dillacorn/QiDi_Plus4/Fluidd/gcode_macro.cfg

# QIDI Plus4 V1.0.0

[gcode_macro _CG28]
description: Safely establish XYZ homing only when needed
gcode:
    {% set homed = printer.toolhead.homed_axes %}

    # If either XY axis is unknown, use QIDI's complete safe
    # X/Y/X and Z homing sequence.
    {% if "x" not in homed or "y" not in homed %}
        G28

    # When XY is already established, home only Z.
    {% elif "z" not in homed %}
        G28 Z
    {% endif %}

[gcode_macro _CXY28]
description: Safely establish XY homing only when needed. Never homes Z.
gcode:
    {% set homed = printer.toolhead.homed_axes %}

    # If either XY axis is unknown, always preserve QIDI's
    # safe X-first X/Y/X homing sequence.
    {% if "x" not in homed or "y" not in homed %}
        G28 X
        G28 Y
        G28 X
    {% endif %}

[gcode_macro zoffset]
gcode:
    SET_GCODE_OFFSET Z={printer.probe.last_z_result} MOVE=1

# Z-offset test helper
[gcode_macro test_zoffset]
gcode:
    G28
    get_zoffset
    G1 X{150 - printer.probe["x_offset"]} Y{150 - printer.probe["y_offset"]} F9000
    G1 Z10 F600
    probe
    M400
    G4 P5000
    G1 Z10 F600

[gcode_macro move_subzoffset]
gcode:
    {% set z = printer.probe.last_z_result|float %}
    {% set z_min = printer.configfile.settings['stepper_z'].position_min|float %}

    {% if z < (z_min + 0.10) %}
        { action_raise_error("Refusing move_subzoffset: suspicious probe result " ~ z ~ " is too close to position_min " ~ z_min) }
    {% endif %}

    G1 Z{z} F600

[gcode_macro get_zoffset]
gcode:
    # TOGGLE_CHAMBER_FAN
    G1 Z10 F600
    Z_VIBRATE
    QIDI_PROBE_PIN_1
    M204 S50
    G4 P500
    probe probe_speed=5 lift_speed=18 samples=5 sample_retract_dist=10
    move_subzoffset
    M114
    {% set p = (-0.15 + printer.gcode_move.homing_origin.z)|float %}
    SET_KINEMATIC_POSITION Z={p}
    G1 Z30 F600
    QIDI_PROBE_PIN_2
    M204 S8800
    # TOGGLE_CHAMBER_FAN

[gcode_macro save_zoffset]
gcode:
    # {% if printer.gcode_move.homing_origin.z < 0.5 %}
    #    SAVE_VARIABLE VARIABLE=z_offset VALUE={printer.gcode_move.homing_origin.z}
    # {% endif %}

[gcode_macro set_zoffset]        
gcode:
    {% set z = printer.save_variables.variables.z_offset %}
    SET_GCODE_OFFSET Z={z} MOVE=0

# Power-loss recovery nozzle clear.
[gcode_macro CLEAR_NOZZLE_PLR]
gcode:
    {% set hotendtemp = params.HOTEND|default(250)|int %}
    {% if (printer.gcode_move.position.z ) < 35 %}
        G1 Z35 F900
    {% else %}
        G91
        G1 Z{5} F900 
        G90
    {% endif %}
    G1 X56 F12000
    G1 Y310 F12000
    G1 Y324 F600
    G1 X95 F600
    M400

    M106 S0
    M109 S{hotendtemp}

    G92 E0
    G1 E5 F50
    G92 E0
    G1 E80 F200
    G92 E0
    G1 E-2 F200
    G4 P300

    M106 S255
    G1 Y316 F30000
    G1 Y320 F3000
    G1 Y316 F30000
    G1 Y320 F3000
    G1 Y316 F30000
    G1 Y320 F3000
    G1 Y316 F12000
    G1 Y312 F600

[gcode_macro CLEAR_NOZZLE]
gcode:
    {% set hotendtemp = params.HOTEND|default(250)|int %}
    {% set purge = params.PURGE|default(1)|int %}
    {% if (printer.gcode_move.position.z ) < 35 %}
        G1 Z35 F900
    {% else %}
        G91
        G1 Z{5} F900 
        G90
    {% endif %}
    G1 X56 F12000
    G1 Y310 F12000
    G1 Y324 F600
    G1 X95 F600
    M400
    {% if purge == 1 %}
        M109 S{hotendtemp}
        G92 E0
        G1 E5 F50
        G92 E0
        G1 E80 F200
        G92 E0
        G1 E-2 F200
    {% else %}
        M104 S140
        G92 E0
        M118 CLEAR_NOZZLE: purge skipped, PEI wipe/cooldown only
    {% endif %}

    M106 S255
    G4 P5000
    M104 S140
    G1 Y318 F9000
    G1 Y322 F600
    G1 Y318 F9000
    G1 Y322 F600
    G1 Y308 F30000
    G1 Y324 F600

    G1 X124 E-1 F1000 

    TEMPERATURE_WAIT SENSOR=extruder MAXIMUM={170}

    G1 X133 F200
    G1 Y321 F200
    G2 I0.5 J0.5 F600
    G2 I0.5 J0.5 F600
    G2 I0.5 J0.5 F600

    G1 Y319 F150
    G1 X132 
    G1 Y324
    G1 X131 
    G1 Y319
    G1 X130
    G1 Y324
    G1 X129
    G1 Y319

    G1 X113 F200
    G1 Y320
    G1 X125
    G1 X113
    G1 X125
    G2 I0.5 J0.5 F200
    G2 I0.5 J0.5 F200
    G2 I0.5 J0.5 F200    

    G1 Y300 F600
    G1 X95 F12000
    G1 Y314 F9000
    G1 Y324 F600

    G1 X58 F12000
    G1 X78 F12000
    G1 Y324
    G1 X58 F12000
    G1 X78 F12000
    G1 Y323.5
    G1 X58 F12000
    G1 X78 F12000
    G1 Y323
    G1 X58 F12000
    G1 X78 F12000
    G1 Y322.5
    G1 X58 F12000
    G1 X78 F12000
    G1 Y322
    G1 X58 F12000
    G1 X75 F12000
    G1 Y321.5
    G2 I0.8 J0.8 F600
    G2 I0.8 J0.8 F600
    G2 I0.8 J0.8 F600

    G1 Y324 F600

    M106 S0

    G1 X95 F12000
    G1 Y316 F9000
    G1 Y312 F600

    M400
    M118 Nozzle cleared
    G1 Y10 F12000
    G1 X10 F12000
    TEMPERATURE_WAIT SENSOR=extruder MAXIMUM={150}
    M107
    M106 P2 S0
    M400
    M118 Nozzle cooled


[gcode_macro MOVE_TO_TRASH]
description: Establish XYZ before entering the purge area
gcode:
    _CG28
    _MOVE_TO_TRASH_AFTER_HOME


[gcode_macro _MOVE_TO_TRASH_AFTER_HOME]
description: Enter the purge area after XYZ homing has completed
gcode:
    {% set homed = printer.toolhead.homed_axes %}

    {% if "x" not in homed or "y" not in homed or "z" not in homed %}
        { action_raise_error("MOVE_TO_TRASH refused: XYZ homing did not complete") }
    {% endif %}

    M204 S8800
    G90

    # On the Plus4, increasing Z lowers the bed away from the nozzle.
    {% if (printer.gcode_move.position.z|float) < 35 %}
        G1 Z35 F900
    {% endif %}

    {% if (printer.gcode_move.position.y|float) > 305 %}
        G1 X82.5 Y324 F6000
        G1 X95 F6000
    {% else %}
        G1 X82.5 F12000
        G1 Y310 F12000
        G1 Y324 F600
        G1 X95 F6000
    {% endif %}

[gcode_macro EXTRUSION_AND_FLUSH]
gcode:
    {% set hotendtemp = params.HOTEND|int %}
    MOVE_TO_TRASH
    M109 S{hotendtemp}
    M83
    G1 E1 F50
    G1 E28.13 F611
    G1 E0.97 F50
    G1 E8.73 F611
    G1 E0.97 F50
    G1 E8.73 F611
    G1 E0.97 F50
    G1 E-2 F1800
    {% for i in range(1,5) %}
        M106 S255
        M400
        G4 P6000
        CLEAR_FLUSH
        M106 S60
        G1 E34.8 F611
        G1 E1.2 F50
        G1 E10.8 F611
        G1 E1.2 F50
        G1 E10.8 F611
        G1 E1.2 F50
        G1 E-2 F1800
    {% endfor %}
    M106 S255
    M400
    G4 P6000
    CLEAR_FLUSH
    M106 S60

[delayed_gcode POSTPRINT_CHAMBER_FAN_OFF]
initial_duration: 0
gcode:
    SET_FAN_SPEED FAN=chamber_circulation_fan SPEED=0.0
    SET_GCODE_VARIABLE MACRO=PRINT_END VARIABLE=postprint_chamber_exhaust VALUE=0
    SET_IDLE_TIMEOUT TIMEOUT={printer.configfile.settings.idle_timeout.timeout}
    RESPOND TYPE=command MSG="POSTPRINT: chamber exhaust OFF"

[gcode_macro START_POSTPRINT_CHAMBER_EXHAUST]
variable_duration: 7200
gcode:
    {% set duration = params.DURATION|default(printer["gcode_macro START_POSTPRINT_CHAMBER_EXHAUST"].duration)|int %}
    {% set normal_idle = printer.configfile.settings.idle_timeout.timeout|int %}
    {% set hold_idle = [normal_idle, duration + 300]|max %}

    UPDATE_DELAYED_GCODE ID=POSTPRINT_CHAMBER_FAN_OFF DURATION=0
    SET_IDLE_TIMEOUT TIMEOUT={hold_idle}
    SET_FAN_SPEED FAN=chamber_circulation_fan SPEED=1.0
    RESPOND TYPE=command MSG="POSTPRINT: chamber exhaust ON for {duration}s"
    UPDATE_DELAYED_GCODE ID=POSTPRINT_CHAMBER_FAN_OFF DURATION={duration}

[gcode_macro STOP_POSTPRINT_CHAMBER_EXHAUST]
gcode:
    UPDATE_DELAYED_GCODE ID=POSTPRINT_CHAMBER_FAN_OFF DURATION=0
    SET_FAN_SPEED FAN=chamber_circulation_fan SPEED=0.0
    SET_GCODE_VARIABLE MACRO=PRINT_END VARIABLE=postprint_chamber_exhaust VALUE=0
    SET_IDLE_TIMEOUT TIMEOUT={printer.configfile.settings.idle_timeout.timeout}
    RESPOND TYPE=command MSG="POSTPRINT: chamber exhaust OFF"

[gcode_macro SCREWS_TILT_CALCULATE]
rename_existing: _SCREWS_TILT_CALCULATE_BASE
gcode:
    { action_respond_info("starting screw rotation calculation...") }

    {% set chamber_target = 0 %}
    {% if printer["heater_generic chamber"] is defined %}
        {% set chamber_target = printer["heater_generic chamber"].target|int %}
    {% endif %}

    {% if chamber_target > 0 %}
        M141 S0
        G4 P15000
        { action_respond_info("Chamber heater temporarily disabled for probing") }
    {% endif %}

    M4031
    G28
    _SCREWS_TILT_CALCULATE_BASE horizontal_move_z=5 sample_retract_dist=8 samples=3

    {% if chamber_target > 0 %}
        M141 S{chamber_target}
        { action_respond_info("Chamber heater restored to " ~ chamber_target ~ "C") }
    {% endif %}

[gcode_macro SET_PRINT_STATS_INFO]
rename_existing: SET_PRINT_STATS_INFO_BASE
gcode:
    {% set curlayer = params.CURRENT_LAYER|default(-1)|int %}

    {% if printer["heater_generic chamber"] is defined
          and curlayer >= 0
          and (printer.toolhead.position.z|float) >= 268.0
          and (printer["heater_generic chamber"].target|float) > 10.0 %}
        M141 S10
    {% endif %}

    SET_PRINT_STATS_INFO_BASE {% for p in params %}{'%s=%s ' % (p, params[p])}{% endfor %}

# Runs before the sliced file starts printing.
[gcode_macro PRINT_START]
gcode:
    # Startup guard: CANCEL_PRINT skips motion during homing/probing failures.
    SET_GCODE_VARIABLE MACRO=_STARTUP_CANCEL_GUARD VARIABLE=active VALUE=1

    # Startup cleanup.
    AUTOTUNE_SHAPERS
    TOOL_CHANGE_END
    DISABLE_ALL_SENSOR
    CLEAR_PAUSE
    STOP_POSTPRINT_CHAMBER_EXHAUST

    # Slicer parameters.
    {% set bedtemp = params.BED|int %}
    {% set hotendtemp = params.HOTEND|int %}
    {% set purgetemp = params.PURGETEMP|default(hotendtemp)|int %}
    {% set chambertemp = params.CHAMBER|default(0)|int %}
    {% set extruder = params.EXTRUDER|default(0)|int %}
    {% set ams_mode = params.AMS|default(1)|int %}
    {% set startup_flush = params.STARTUP_FLUSH|default("AUTO")|string|upper %}

    # QiDi Box / AMS saved state for requested tool/slot.
    {% set sv = printer.save_variables.variables %}
    {% set requested_slot = sv["value_t" ~ extruder]|default("slot" ~ extruder) %}
    {% set slot_sync_before = sv.slot_sync|default("slot-1") %}
    {% set last_load_slot = sv.last_load_slot|default("slot-1") %}
    {% set requested_slot_already_loaded = (slot_sync_before == requested_slot and last_load_slot == requested_slot) %}

    {% set force_startup_flush = startup_flush in ["1", "YES", "TRUE", "FULL", "FORCE"] %}
    {% set skip_startup_flush = startup_flush in ["0", "NO", "FALSE", "SKIP", "OFF", "NONE"] %}
    {% set full_startup_flush = (ams_mode == 1 and (force_startup_flush or ((not requested_slot_already_loaded) and (not skip_startup_flush)))) %}

    # Track chamber use so PRINT_END can run post-print exhaust.
    {% if chambertemp > 0 %}
        SET_GCODE_VARIABLE MACRO=PRINT_END VARIABLE=postprint_chamber_exhaust VALUE=1
    {% else %}
        SET_GCODE_VARIABLE MACRO=PRINT_END VARIABLE=postprint_chamber_exhaust VALUE=0
    {% endif %}

    # Known heater/fan startup state.
    M104 S0
    M106 P2 S0
    M106 S255

    # Keep chamber and box heat off during startup calibration.
    M141 S0
    DISABLE_BOX_HEATER
    SET_FAN_SPEED FAN=chamber_circulation_fan SPEED=0.0

    # If already homed, move away from the parked corner before homing again.
    {% if "xyz" in printer.toolhead.homed_axes %}
        G0 X50 Y50 F6000
    {% endif %}

    # Home before AMS/trash-bin motion.
    G28

    # Heat and wait for the bed before Z calibration.
    M140 S{bedtemp}
    M106 S0
    WAIT_BED_LOG S={bedtemp}

    # AMS / QiDi Box startup happens before nozzle cleaning and Z calibration.
    {% if ams_mode == 1 %}
        {% set box_count = printer.save_variables.variables.box_count|default(0)|int %}
        {% set enable_box = printer.save_variables.variables.enable_box|default(0)|int %}

        M118 PRINT_START: AMS=1 requested_tool={extruder} box_count={box_count} enable_box={enable_box}

        {% if box_count < 1 %}
            SET_GCODE_VARIABLE MACRO=_STARTUP_CANCEL_GUARD VARIABLE=active VALUE=0
            { action_raise_error("AMS startup refused: box_count is " ~ box_count ~ ", expected >= 1") }
        {% endif %}

        {% if enable_box != 1 %}
            SET_GCODE_VARIABLE MACRO=_STARTUP_CANCEL_GUARD VARIABLE=active VALUE=0
            { action_raise_error("AMS startup refused: enable_box is " ~ enable_box ~ ", expected 1") }
        {% endif %}

        # Reset QiDi Box startup state.
        SAVE_VARIABLE VARIABLE=load_retry_num VALUE=0
        SAVE_VARIABLE VARIABLE=retry_step VALUE=None
        SAVE_VARIABLE VARIABLE=is_tool_change VALUE=0

        # Clear saved runout states.
        {% for i in range(16) %}
            SAVE_VARIABLE VARIABLE=runout_{i} VALUE=0
            G4 P100
        {% endfor %}

        SAVE_VARIABLE VARIABLE=extrude_state VALUE=-1

        M118 PRINT_START: requested_tool={extruder} requested_slot={requested_slot} slot_sync_before={slot_sync_before} last_load_slot={last_load_slot} startup_flush={startup_flush}

        # Select/load the actual requested starting tool before Z calibration.
        BOX_PRINT_START EXTRUDER={extruder} HOTENDTEMP={purgetemp}
        M400

        {% if force_startup_flush %}
            M118 PRINT_START: forcing full startup EXTRUSION_AND_FLUSH
            EXTRUSION_AND_FLUSH HOTEND={purgetemp}

        {% elif skip_startup_flush %}
            M118 PRINT_START: skipping startup EXTRUSION_AND_FLUSH by slicer request

        {% elif requested_slot_already_loaded %}
            M118 PRINT_START: skipping startup EXTRUSION_AND_FLUSH, {requested_slot} was already loaded

        {% else %}
            M118 PRINT_START: full startup EXTRUSION_AND_FLUSH, requested slot was not already loaded
            EXTRUSION_AND_FLUSH HOTEND={purgetemp}
        {% endif %}

    {% else %}
        M118 PRINT_START: AMS=0, skipping QiDi Box startup
    {% endif %}

    M106 S0

    # Probe prep:
    # - If a full AMS startup flush already ran, skip the big CLEAR_NOZZLE purge,
    #   but still run CLEAR_NOZZLE in no-purge mode so the PEI rub/cooldown happens.
    # - If no full flush ran, use normal CLEAR_NOZZLE so probing starts with a clean nozzle.
    {% if full_startup_flush %}
        M118 PRINT_START: startup flush completed, doing no-purge CLEAR_NOZZLE PEI wipe
        M106 S255
        CLEAR_FLUSH
        CLEAR_OOZE
        CLEAR_NOZZLE HOTEND={purgetemp} PURGE=0
        M106 S0
    {% else %}
        M118 PRINT_START: clearing loaded nozzle before Z_TILT/G29 probing
        CLEAR_NOZZLE HOTEND={purgetemp}
    {% endif %}

    # Hold a low nozzle temp during probing to reduce new ooze.
    M104 S140

    # Full QIDI-style Z calibration.
    # Pre-position at the first Z-tilt point while the bed is still down/away.
    # This avoids a bed-up travel move from the trash/wipe area to the first probe point.
    M118 PRINT_START: running Z_TILT_ADJUST + G32/G29
    G90
    {% if (printer.gcode_move.position.z|float) < 35 %}
        G1 Z35 F900
    {% endif %}
    G1 X0 Y138.5 F9000
    M400
    M118 PRINT_START: pre-positioned at first Z_TILT point X0 Y138.5 before probing
    Z_TILT_ADJUST
    G32
    G29

    # Park after Z calibration.
    G0 Z50 F600
    G0 X5 Y5 F6000

    # Restore chamber heat after Z calibration and AMS startup.
    {% if chambertemp > 0 %}
        M141 S{chambertemp}
        SET_FAN_SPEED FAN=chamber_circulation_fan SPEED=0.70
    {% else %}
        M141 S0
        SET_FAN_SPEED FAN=chamber_circulation_fan SPEED=0.0
    {% endif %}

    # Final hotend heat.
    M109 S{hotendtemp}

    # Final print-state setup.
    M204 S8800
    SET_PRINT_STATS_INFO CURRENT_LAYER=1
    SET_GCODE_VARIABLE MACRO=_STARTUP_CANCEL_GUARD VARIABLE=active VALUE=0

    # Re-enable the correct filament sensors.
    {% if ams_mode == 1 %}
        ENABLE_ALL_SENSOR
    {% else %}
        SET_FILAMENT_SENSOR SENSOR=fila ENABLE=1
        {% if printer["filament_motion_sensor box_motion_sensor"] %}
            SET_FILAMENT_SENSOR SENSOR=box_motion_sensor ENABLE=0
        {% endif %}
        DISABLE_FILAMENT_WIDTH_SENSOR
        RESET_FILAMENT_WIDTH_SENSOR
    {% endif %}

    # Arm guard for Orca's startup T# command after PRINT_START.
    # PRINT_START already loaded the requested startup tool.
    # The first matching T# after PRINT_START should be skipped once.
    {% if ams_mode == 1 %}
        SET_GCODE_VARIABLE MACRO=_STARTUP_TOOL_GUARD VARIABLE=active VALUE=1
        SET_GCODE_VARIABLE MACRO=_STARTUP_TOOL_GUARD VARIABLE=tool VALUE={extruder}
    {% else %}
        SET_GCODE_VARIABLE MACRO=_STARTUP_TOOL_GUARD VARIABLE=active VALUE=0
        SET_GCODE_VARIABLE MACRO=_STARTUP_TOOL_GUARD VARIABLE=tool VALUE=-1
    {% endif %}

    # Save current file/temp state for power-loss recovery.
    save_last_file
    
[gcode_macro ENABLE_ALL_SENSOR]
gcode:
    SET_FILAMENT_SENSOR SENSOR=fila ENABLE=1
    {% if printer["filament_motion_sensor box_motion_sensor"] and printer.save_variables.variables.enable_box|default(0)|int == 1 %}
        CLEAR_MOTION_DATA SENSOR=box_motion_sensor
        SET_FILAMENT_SENSOR SENSOR=box_motion_sensor ENABLE=1
    {% endif %}

[gcode_macro DISABLE_ALL_SENSOR]
gcode:
    SET_FILAMENT_SENSOR SENSOR=fila ENABLE=0
    {% if printer["filament_motion_sensor box_motion_sensor"] %}
        SET_FILAMENT_SENSOR SENSOR=box_motion_sensor ENABLE=0
    {% endif %}
    DISABLE_FILAMENT_WIDTH_SENSOR
    RESET_FILAMENT_WIDTH_SENSOR

[gcode_macro AUTOTUNE_SHAPERS]
variable_autotune_shapers: 'ei'
gcode:

[gcode_macro _HOMING_GUARD]
variable_active: 0
gcode:

[gcode_macro _STARTUP_TOOL_GUARD]
variable_active: 0
variable_tool: -1
gcode:

[gcode_macro _STARTUP_CANCEL_GUARD]
variable_active: 0
gcode:

[gcode_macro M84]
rename_existing:M84.1
gcode:
    M84.1
        SET_STEPPER_ENABLE STEPPER=stepper_x enable=0
        SET_STEPPER_ENABLE STEPPER=stepper_y enable=0
        SET_STEPPER_ENABLE STEPPER=stepper_z enable=1
    SET_STEPPER_ENABLE STEPPER=stepper_z1 enable=1
        SET_STEPPER_ENABLE STEPPER=extruder enable=0

# Power-loss recovery detection.
[gcode_macro DETECT_INTERRUPTION]
gcode:
    {% set was_interrupted = printer.save_variables.variables.was_interrupted %}
    {% if was_interrupted %}
    M118 Detected unexpected interruption during the last print. Do you want to resume printing? (Do not move the extruder before resuming.)
    M118 Yes: RESUME_INTERRUPTED
    M118 No: CLEAR_LAST_FILE
    {% endif %}

# Runs when Klipper initializes.
[delayed_gcode PRINTER_INIT]
initial_duration:0.2
gcode:
        SET_STEPPER_ENABLE STEPPER=stepper_z enable=1
    SET_STEPPER_ENABLE STEPPER=stepper_z1 enable=1
    BED_MESH_CLEAR      
    DISABLE_ALL_SENSOR
    SET_GCODE_VARIABLE MACRO=_HOMING_GUARD VARIABLE=active VALUE=0
    SET_GCODE_VARIABLE MACRO=_STARTUP_CANCEL_GUARD VARIABLE=active VALUE=0
    SET_GCODE_VARIABLE MACRO=_STARTUP_TOOL_GUARD VARIABLE=active VALUE=0
    SET_GCODE_VARIABLE MACRO=_STARTUP_TOOL_GUARD VARIABLE=tool VALUE=-1

[gcode_macro _RESTORE_CHAMBER_AFTER_HOME]
variable_target: 0
gcode:
    {% set saved = printer["gcode_macro _RESTORE_CHAMBER_AFTER_HOME"].target|int %}
    {% if saved > 0 %}
        M141 S{saved}
        { action_respond_info("Chamber heater restored to " ~ saved ~ "C after homing") }
        SET_GCODE_VARIABLE MACRO=_RESTORE_CHAMBER_AFTER_HOME VARIABLE=target VALUE=0
    {% endif %}

[delayed_gcode _RESTORE_CHAMBER_AFTER_HOME_DELAYED]
initial_duration: 0
gcode:
    _RESTORE_CHAMBER_AFTER_HOME


[homing_override]
axes:xyz
gcode:
    SET_GCODE_VARIABLE MACRO=_HOMING_GUARD VARIABLE=active VALUE=1
    UPDATE_DELAYED_GCODE ID=_RESTORE_CHAMBER_AFTER_HOME_DELAYED DURATION=0

    {% set chamber_target = 0 %}
    {% if printer["heater_generic chamber"] is defined %}
        {% set chamber_target = printer["heater_generic chamber"].target|int %}
    {% endif %}
    SET_GCODE_VARIABLE MACRO=_RESTORE_CHAMBER_AFTER_HOME VARIABLE=target VALUE={chamber_target}

    {% set HOME_CUR = 1 %}
    {% set driver_config = printer.configfile.settings['tmc2240 stepper_x'] %}
    {% set RUN_CUR = driver_config.run_current %}
    {% set HOLD_CUR = driver_config.hold_current %}
    {% set x_center = (printer.toolhead.axis_maximum.x|float / 2) %}
    {% set y_center = (printer.toolhead.axis_maximum.y|float / 2) %}
    M204 S8800
    M220 S100

    {% if params.X is defined %}
        SET_TMC_CURRENT STEPPER=stepper_x CURRENT={HOME_CUR * 0.7}
        G28 X
        SET_TMC_CURRENT STEPPER=stepper_x CURRENT={HOME_CUR}
        BEEP I=1 DUR=100
        G90
        G1 X10 F1200
    {% endif %}

    {% if params.Y is defined %}
        SET_TMC_CURRENT STEPPER=stepper_y CURRENT={HOME_CUR * 0.9}
        G28 Y
        SET_TMC_CURRENT STEPPER=stepper_y CURRENT={HOME_CUR}
        BEEP I=1 DUR=100
        G90
        G1 Y10 F1200
    {% endif %}

    {% if params.Z is defined %}
        {% set homed = printer.toolhead.homed_axes %}

        # Z homing requires known XY coordinates.
        # If either XY axis is unknown, preserve QIDI's safe
        # X-first X/Y/X homing sequence.
        {% if "x" not in homed or "y" not in homed %}
            G28 X
            G28 Y
            G28 X
        {% endif %}

        G90
        G1 X{x_center} Y{y_center} F7800

        SET_KINEMATIC_POSITION Z={printer.toolhead.axis_maximum.z-30}
        QIDI_PROBE_PIN_2
        PROBE SAMPLES=2
        SET_KINEMATIC_POSITION Z=1.9
        G1 Z10 F600
        Z_VIBRATE
        QIDI_PROBE_PIN_1
        PROBE PROBE_SPEED=10
        SET_KINEMATIC_POSITION Z=-0.1
        G91
        G1 Z30 F480
        G90
        G1 X{x_center} Y{y_center} F7800
    {% endif %}

    {% if params.X is undefined %}
    {% if params.Y is undefined %}
    {% if params.Z is undefined %}
        SET_KINEMATIC_POSITION X=0
        SET_KINEMATIC_POSITION Y=0
        SET_KINEMATIC_POSITION Z={printer.toolhead.axis_maximum.z-30}
        G91
        G1 Z7 F600
        G1 X5 F2400
        G1 Y5 F2400
        G4 P2000

        SET_TMC_CURRENT STEPPER=stepper_x CURRENT={HOME_CUR * 0.8}
        G28 X
        SET_TMC_CURRENT STEPPER=stepper_x CURRENT={HOME_CUR}
        BEEP I=1 DUR=100
        G90
        G1 X45 F1200

        SET_TMC_CURRENT STEPPER=stepper_y CURRENT={HOME_CUR * 0.9}
        G28 Y
        SET_TMC_CURRENT STEPPER=stepper_y CURRENT={HOME_CUR}
        BEEP I=1 DUR=100
        G90
        G1 Y10 F1200

        SET_TMC_CURRENT STEPPER=stepper_x CURRENT={HOME_CUR * 0.8}
        G28 X
        SET_TMC_CURRENT STEPPER=stepper_x CURRENT={HOME_CUR}
        BEEP I=1 DUR=100
        G90
        G1 X10 F1200

        SET_KINEMATIC_POSITION Z={printer.toolhead.axis_maximum.z-10}

        G90
        G1 X{x_center} Y{y_center} F7800
        QIDI_PROBE_PIN_2
        G28 Z
        G91
        G1 Z30 F600
        G90
        G1 X{x_center} Y{y_center} F7800
    {% endif %}
    {% endif %}
    {% endif %}

    SET_TMC_CURRENT STEPPER=stepper_x CURRENT={RUN_CUR}
    SET_TMC_CURRENT STEPPER=stepper_y CURRENT={RUN_CUR}
    M204 S8800
    G90
    QIDI_PROBE_PIN_2
    SET_GCODE_VARIABLE MACRO=_HOMING_GUARD VARIABLE=active VALUE=0

    {% if chamber_target > 0 %}
        UPDATE_DELAYED_GCODE ID=_RESTORE_CHAMBER_AFTER_HOME_DELAYED DURATION=1.0
    {% endif %}

[gcode_macro SHAPER_CALIBRATE]
rename_existing: RESHAPER_CALIBRATE
gcode:
    RESHAPER_CALIBRATE FREQ_START=20 FREQ_END=150

[delayed_gcode postprint_chamber_alert_15]
gcode:
    {% if printer["gcode_macro PRINT_END"].postprint_alerts_enabled|int == 1 %}
        SET_PIN PIN=beeper VALUE=1
        G4 P100
        SET_PIN PIN=beeper VALUE=0
        G4 P120
        SET_PIN PIN=beeper VALUE=1
        G4 P100
        SET_PIN PIN=beeper VALUE=0
    {% endif %}

[delayed_gcode postprint_chamber_alert_30]
gcode:
    {% if printer["gcode_macro PRINT_END"].postprint_alerts_enabled|int == 1 %}
        SET_PIN PIN=beeper VALUE=1
        G4 P80
        SET_PIN PIN=beeper VALUE=0
        G4 P100
        SET_PIN PIN=beeper VALUE=1
        G4 P80
        SET_PIN PIN=beeper VALUE=0
        G4 P100
        SET_PIN PIN=beeper VALUE=1
        G4 P80
        SET_PIN PIN=beeper VALUE=0
    {% endif %}
    SET_GCODE_VARIABLE MACRO=PRINT_END VARIABLE=postprint_alerts_enabled VALUE=0

[gcode_macro PRINT_END]
variable_postprint_chamber_exhaust: 0
variable_postprint_alerts_enabled: 0
gcode:
    {% set chamber_print_flag = printer["gcode_macro PRINT_END"].postprint_chamber_exhaust|int %}
    {% set live_chamber_target = 0 %}
    {% if printer["heater_generic chamber"] is defined %}
        {% set live_chamber_target = printer["heater_generic chamber"].target|int %}
    {% endif %}
    {% set postprint_exhaust_needed = 1 if (chamber_print_flag == 1 or live_chamber_target > 0) else 0 %}

    # {% if printer.gcode_move.homing_origin.z < 0.5 %}
    #    SAVE_VARIABLE VARIABLE=z_offset VALUE={printer.gcode_move.homing_origin.z}
    # {% endif %}

    CLEAR_PAUSE
    M400
    G4 P5000
    M106 P2 S0
    M106 P0 S0
    TURN_OFF_HEATERS
    DISABLE_BOX_HEATER

    {% if postprint_exhaust_needed == 1 %}
        START_POSTPRINT_CHAMBER_EXHAUST DURATION=7200
        SET_GCODE_VARIABLE MACRO=PRINT_END VARIABLE=postprint_alerts_enabled VALUE=0
        UPDATE_DELAYED_GCODE ID=postprint_chamber_alert_15 DURATION=0
        UPDATE_DELAYED_GCODE ID=postprint_chamber_alert_30 DURATION=0
    {% else %}
        STOP_POSTPRINT_CHAMBER_EXHAUST
        SET_GCODE_VARIABLE MACRO=PRINT_END VARIABLE=postprint_alerts_enabled VALUE=0
        UPDATE_DELAYED_GCODE ID=postprint_chamber_alert_15 DURATION=0
        UPDATE_DELAYED_GCODE ID=postprint_chamber_alert_30 DURATION=0
    {% endif %}
    SET_GCODE_VARIABLE MACRO=_HOMING_GUARD VARIABLE=active VALUE=0
    SET_GCODE_VARIABLE MACRO=_STARTUP_CANCEL_GUARD VARIABLE=active VALUE=0
    SET_GCODE_VARIABLE MACRO=_STARTUP_TOOL_GUARD VARIABLE=active VALUE=0
    SET_GCODE_VARIABLE MACRO=_STARTUP_TOOL_GUARD VARIABLE=tool VALUE=-1

    M220 S100
    M221 S100
    SET_STEPPER_ENABLE STEPPER=stepper_x ENABLE=0
    SET_STEPPER_ENABLE STEPPER=stepper_y ENABLE=0
    SET_STEPPER_ENABLE STEPPER=stepper_z ENABLE=1
    SET_STEPPER_ENABLE STEPPER=stepper_z1 ENABLE=1
    SET_STEPPER_ENABLE STEPPER=extruder ENABLE=0

    DISABLE_ALL_SENSOR
    BED_MESH_CLEAR
    G31
    CLEAR_LAST_FILE
    M84

[gcode_macro _SAFE_Z_LIFT]
description: Relative Z lift capped by axis max. On Plus4, positive Z lowers the bed away from the nozzle.
gcode:
    {% set lift_req = params.LIFT|default(10)|float %}
    {% set speed = params.SPEED|default(900)|float %}
    {% set homed = printer.toolhead.homed_axes %}

    {% if "z" in homed %}
        {% set z_now = printer.gcode_move.position.z|float %}
        {% set z_max = printer.toolhead.axis_maximum.z|float %}
        {% set lift = [lift_req, z_max - z_now - 2.0]|min %}

        {% if lift > 0.2 %}
            SAVE_GCODE_STATE NAME=SAFE_Z_LIFT_STATE
            G91
            G1 Z{lift} F{speed}
            RESTORE_GCODE_STATE NAME=SAFE_Z_LIFT_STATE
            M400
            RESPOND TYPE=command MSG="SAFE_Z_LIFT: lifted Z by {lift|round(2)}mm"
        {% else %}
            RESPOND TYPE=command MSG="SAFE_Z_LIFT: skipped, not enough Z room"
        {% endif %}
    {% else %}
        RESPOND TYPE=command MSG="SAFE_Z_LIFT: skipped, Z not homed"
    {% endif %}

[gcode_macro CANCEL_PRINT]
rename_existing: BASE_CANCEL_PRINT
gcode:
    {% set chamber_print_flag = printer["gcode_macro PRINT_END"].postprint_chamber_exhaust|int %}
    {% set live_chamber_target = 0 %}
    {% if printer["heater_generic chamber"] is defined %}
        {% set live_chamber_target = printer["heater_generic chamber"].target|int %}
    {% endif %}
    {% set postprint_exhaust_needed = 1 if (chamber_print_flag == 1 or live_chamber_target > 0) else 0 %}
    {% set homing_active = printer["gcode_macro _HOMING_GUARD"].active|int %}
    {% set startup_active = printer["gcode_macro _STARTUP_CANCEL_GUARD"].active|int %}
    {% set homed = printer.toolhead.homed_axes %}

    CLEAR_PAUSE
    BASE_CANCEL_PRINT
    CLEAR_PAUSE

    TURN_OFF_HEATERS
    DISABLE_BOX_HEATER

    M106 P2 S0
    M106 P0 S0

    {% if postprint_exhaust_needed == 1 %}
        START_POSTPRINT_CHAMBER_EXHAUST DURATION=7200
        SET_GCODE_VARIABLE MACRO=PRINT_END VARIABLE=postprint_alerts_enabled VALUE=0
        UPDATE_DELAYED_GCODE ID=postprint_chamber_alert_15 DURATION=0
        UPDATE_DELAYED_GCODE ID=postprint_chamber_alert_30 DURATION=0
    {% else %}
        STOP_POSTPRINT_CHAMBER_EXHAUST
        SET_GCODE_VARIABLE MACRO=PRINT_END VARIABLE=postprint_alerts_enabled VALUE=0
        UPDATE_DELAYED_GCODE ID=postprint_chamber_alert_15 DURATION=0
        UPDATE_DELAYED_GCODE ID=postprint_chamber_alert_30 DURATION=0
    {% endif %}

    M220 S100
    M221 S100

    {% if homing_active == 1 %}
        RESPOND TYPE=command MSG="CANCEL_PRINT: homing active, skipping cancel motion"
    {% else %}
        {% if "z" in homed %}
            _SAFE_Z_LIFT LIFT=25 SPEED=600
        {% else %}
            RESPOND TYPE=command MSG="CANCEL_PRINT: Z not homed, skipping bed drop"
        {% endif %}

        {% if "x" in homed and "y" in homed %}
            G90

            {% if printer.gcode_move.position.y > 307 %}
                RESPOND TYPE=command MSG="CANCEL_PRINT: escaping trash/lever zone"
                G1 Y250 F6000
                M400
            {% endif %}

            {% if startup_active == 1 %}
                RESPOND TYPE=command MSG="CANCEL_PRINT: startup active, skipped full park after safe bed drop"
            {% else %}
                G1 X95 Y290 F7800
                M400
            {% endif %}
        {% else %}
            RESPOND TYPE=command MSG="CANCEL_PRINT: XY not homed, skipped park"
        {% endif %}
    {% endif %}

    save_zoffset

    SET_GCODE_VARIABLE MACRO=_HOMING_GUARD VARIABLE=active VALUE=0
    SET_GCODE_VARIABLE MACRO=_STARTUP_CANCEL_GUARD VARIABLE=active VALUE=0
    SET_GCODE_VARIABLE MACRO=_STARTUP_TOOL_GUARD VARIABLE=active VALUE=0
    SET_GCODE_VARIABLE MACRO=_STARTUP_TOOL_GUARD VARIABLE=tool VALUE=-1

    SET_STEPPER_ENABLE STEPPER=stepper_x ENABLE=0
    SET_STEPPER_ENABLE STEPPER=stepper_y ENABLE=0
    SET_STEPPER_ENABLE STEPPER=stepper_z ENABLE=1
    SET_STEPPER_ENABLE STEPPER=stepper_z1 ENABLE=1
    SET_STEPPER_ENABLE STEPPER=extruder ENABLE=0

    DISABLE_ALL_SENSOR
    BED_MESH_CLEAR
    G31
    M84
    CLEAR_LAST_FILE

[gcode_macro PAUSE]
rename_existing: BASE_PAUSE
gcode:
    {% set z = params.Z|default(35)|int %}

    {% if printer['pause_resume'].is_paused|int == 0 %}     
        SET_GCODE_VARIABLE MACRO=RESUME_PRINT VARIABLE=zhop VALUE={z}
        SET_GCODE_VARIABLE MACRO=RESUME_PRINT VARIABLE=etemp VALUE={printer['extruder'].target}
        SET_GCODE_VARIABLE MACRO=RESUME_PRINT VARIABLE=efan VALUE={printer["fan_generic cooling_fan"].speed *255}

        DISABLE_ALL_SENSOR
        SAVE_GCODE_STATE NAME=PAUSE              
        BASE_PAUSE
        G92 E0
        G1 E-5 F1800
        {% if (printer.gcode_move.position.z ) < z %}
            G91
            G1 Z{z} F900
        {% else %}
            G91
            G1 Z{5} F900 
            SET_GCODE_VARIABLE MACRO=RESUME_PRINT VARIABLE=zhop VALUE=0
        {% endif %}
        SAVE_GCODE_STATE NAME=PAUSEPARK2
        G90
        G1 X95 F12000
        G1 Y312 F12000
        G1 Y316 F600
        G1 Y320 F9000
        G1 Y324 F600
        SAVE_GCODE_STATE NAME=PAUSEPARK
        M104 S0
        SET_IDLE_TIMEOUT TIMEOUT=86400
        SET_STEPPER_ENABLE STEPPER=extruder enable=0
        {% set slot_sync = printer.save_variables.variables.slot_sync|default("slot-1") %}
        {% if printer['box_stepper ' ~ slot_sync] %}
            SET_STEPPER_ENABLE STEPPER="box_stepper {slot_sync}" ENABLE=0
        {% endif %}
    {% endif %}

[gcode_macro RESUME_PRINT]
variable_zhop: 0
variable_etemp: 0
variable_efan: 0
gcode:
    {% set e = params.E|default(5)|int %}
    {% set tool_change = params.TOOL_CHANGE|default(0)|int %}

    {% if printer['pause_resume'].is_paused|int == 1 %}
        {% if printer.save_variables.variables.box_count >= 1 and printer.save_variables.variables.enable_box == 1 and printer.save_variables.variables.is_tool_change == 1%} 
            SET_IDLE_TIMEOUT TIMEOUT={printer.configfile.settings.idle_timeout.timeout}
            MOVE_TO_TRASH
            {% if etemp > 0 %}
                M109 S{etemp|int}
            {% endif %}
            M83
            RESTORE_GCODE_STATE NAME=PAUSEPARK2 MOVE=1 MOVE_SPEED=200                            
            RESTORE_GCODE_STATE NAME=PAUSE MOVE=1 MOVE_SPEED=15
            BASE_RESUME  
        {% else %}
            SET_IDLE_TIMEOUT TIMEOUT={printer.configfile.settings.idle_timeout.timeout}
            {% if etemp > 0 %}
                M109 S{etemp|int}
            {% endif %}
            {% if printer.save_variables.variables.box_count >= 1 %} 
                SAVE_VARIABLE VARIABLE=retry_step VALUE=None
            {% endif %}
            M83              
            M106 S0
            G1 X95 F12000
            G1 Y324 F12000                
            G92 E0
            G1 E5 F50
            G92 E0
            G1 E50 F200
            G92 E0
            G1 E-0.8 F200
            G4 P300

            M106 S{efan}

            G1 Y318 F30000
            G1 Y322 F3000
            G1 Y318 F30000
            G1 Y322 F3000
            G1 Y318 F30000
            G1 Y322 F3000
            G1 Y324 F600

            G1 X58 F12000
            G1 X78 F12000
            G1 X58 F12000
            G1 X78 F12000
            G1 X58 F12000
            G1 X78 F12000
            G1 X58 F12000
            G1 X78 F12000
            G1 X58 F12000
            G1 X78 F12000
            G1 X58 F12000
            G1 X78 F12000
            G1 X95 F12000

            G1 Y316 F9000
            G1 Y312 F600
            G1 Y260 F12000 
            RESTORE_GCODE_STATE NAME=PAUSEPARK2 MOVE=1 MOVE_SPEED=200                            
            RESTORE_GCODE_STATE NAME=PAUSE MOVE=1 MOVE_SPEED=15
            BASE_RESUME  
            {% if tool_change == 0 %}
                ENABLE_ALL_SENSOR
            {% endif %}
        {% endif %}
    {% endif %}

[gcode_macro RESUME]
rename_existing: BASE_RESUME
gcode:
    {% if printer['pause_resume'].is_paused|int == 1 %}
        {% if printer["filament_switch_sensor fila"].enabled %}
            {% if printer["filament_switch_sensor fila"].filament_detected %}
                RESUME_PRINT
            {% else %}
                M118 Printer resume failed: fila reports no filament
            {% endif %}
        {% else %}
            M118 RESUME: fila sensor disabled, resuming without filament check
            RESUME_PRINT
        {% endif %}
    {% endif %}

[gcode_macro BEEP]
gcode:
    {% set i = params.I|default(1)|int %}
    {% set dur = params.DUR|default(100)|int %}

    {% if printer["output_pin sound"].value|int == 1 %}
        {% for iteration in range(i|int) %}
            SET_PIN PIN=beeper VALUE=1
            G4 P{dur}
            SET_PIN PIN=beeper VALUE=0
                    G4 P{dur}
        {% endfor %}
    {% endif %}

[gcode_macro TEMP_REACHED_STATE]
variable_bed_announced: 0
variable_chamber_announced: 0
gcode:

[gcode_macro SET_HEATER_TEMPERATURE]
rename_existing: BASE_SET_HEATER_TEMPERATURE
description: Set heater target and announce when reached for bed and chamber
gcode:
    {% set heater = params.HEATER|string %}
    {% set target_in = params.TARGET|default(0)|float %}
    {% if heater == "chamber" %}
        {% set target = ([target_in, 65]|min) %}
    {% else %}
        {% set target = target_in %}
    {% endif %}

    BASE_SET_HEATER_TEMPERATURE HEATER={heater} TARGET={target}

    {% if heater == "heater_bed" %}
        {% if target > 0 %}
            SET_GCODE_VARIABLE MACRO=TEMP_REACHED_STATE VARIABLE=bed_announced VALUE=0
            { action_respond_info("Bed: heating to " ~ target ~ "C") }
            UPDATE_DELAYED_GCODE ID=BED_REACHED_WATCH DURATION=1
        {% else %}
            SET_GCODE_VARIABLE MACRO=TEMP_REACHED_STATE VARIABLE=bed_announced VALUE=0
            UPDATE_DELAYED_GCODE ID=BED_REACHED_WATCH DURATION=0
        {% endif %}
    {% elif heater == "chamber" and printer["heater_generic chamber"] is defined %}
        {% if target > 0 %}
            SET_GCODE_VARIABLE MACRO=TEMP_REACHED_STATE VARIABLE=chamber_announced VALUE=0
            { action_respond_info("Chamber: heating to " ~ target ~ "C") }
            UPDATE_DELAYED_GCODE ID=CHAMBER_REACHED_WATCH DURATION=1
        {% else %}
            SET_GCODE_VARIABLE MACRO=TEMP_REACHED_STATE VARIABLE=chamber_announced VALUE=0
            UPDATE_DELAYED_GCODE ID=CHAMBER_REACHED_WATCH DURATION=0
        {% endif %}
    {% endif %}

[gcode_macro M140]
rename_existing: M99140
description: Set bed target and announce when reached
gcode:
    {% set s = params.S|default(0)|float %}

    M99140 {% for p in params %}{'%s%s ' % (p, params[p])}{% endfor %}

    {% if s > 0 %}
        SET_GCODE_VARIABLE MACRO=TEMP_REACHED_STATE VARIABLE=bed_announced VALUE=0
        { action_respond_info("Bed: heating to " ~ s ~ "C") }
        UPDATE_DELAYED_GCODE ID=BED_REACHED_WATCH DURATION=1
    {% else %}
        SET_GCODE_VARIABLE MACRO=TEMP_REACHED_STATE VARIABLE=bed_announced VALUE=0
        UPDATE_DELAYED_GCODE ID=BED_REACHED_WATCH DURATION=0
    {% endif %}

[gcode_macro M141]
gcode:
    {% if printer["heater_generic chamber"] is defined %}
        {% set s = params.S|default(0)|float %}
        {% set target = ([s, 65]|min) %}
        SET_HEATER_TEMPERATURE HEATER=chamber TARGET={target}

        # {% if printer['heater_bed'].target < s+25 and s!=0 %}
        #     M140 S{s+25}
        #     M118 If the heatbed is below {s+25} degrees, the heatbed temperature will be automatically set to {s+25}.
        # {% endif %}
    {% endif %}

[delayed_gcode BED_REACHED_WATCH]
initial_duration: 0
gcode:
    {% set bed = printer.heater_bed %}
    {% set state = printer["gcode_macro TEMP_REACHED_STATE"] %}

    {% if bed.target > 0 and state.bed_announced|int == 0 %}
        {% if bed.temperature >= (bed.target - 0.2) %}
            { action_respond_info("Bed: target " ~ (bed.target|round(1)) ~ "C reached, sensor " ~ (bed.temperature|round(1)) ~ "C") }
            SET_GCODE_VARIABLE MACRO=TEMP_REACHED_STATE VARIABLE=bed_announced VALUE=1
        {% else %}
            UPDATE_DELAYED_GCODE ID=BED_REACHED_WATCH DURATION=1
        {% endif %}
    {% endif %}

[delayed_gcode CHAMBER_REACHED_WATCH]
initial_duration: 0
gcode:
    {% if printer["heater_generic chamber"] is defined %}
        {% set chamber = printer["heater_generic chamber"] %}
        {% set state = printer["gcode_macro TEMP_REACHED_STATE"] %}

        {% if chamber.target > 0 and state.chamber_announced|int == 0 %}
            {% if chamber.temperature >= (chamber.target - 0.5) %}
                { action_respond_info("Chamber: target " ~ (chamber.target|round(1)) ~ "C reached, sensor " ~ (chamber.temperature|round(1)) ~ "C") }
                SET_GCODE_VARIABLE MACRO=TEMP_REACHED_STATE VARIABLE=chamber_announced VALUE=1
            {% else %}
                UPDATE_DELAYED_GCODE ID=CHAMBER_REACHED_WATCH DURATION=1
            {% endif %}
        {% endif %}
    {% endif %}

[gcode_macro WAIT_BED_LOG]
description: Set/wait for bed and print console status without relying on QIDI M190 behavior.
gcode:
    {% set s = params.S|float %}

    SET_GCODE_VARIABLE MACRO=TEMP_REACHED_STATE VARIABLE=bed_announced VALUE=0
    UPDATE_DELAYED_GCODE ID=BED_REACHED_WATCH DURATION=0

    {% if s > 0 %}
        M140 S{s}
        M118 Bed: waiting for {s}C
        TEMPERATURE_WAIT SENSOR=heater_bed MINIMUM={s - 0.2}
        SET_GCODE_VARIABLE MACRO=TEMP_REACHED_STATE VARIABLE=bed_announced VALUE=1
        M118 Bed: target {s}C reached, sensor {printer.heater_bed.temperature|round(1)}C
    {% else %}
        M140 S0
        SET_GCODE_VARIABLE MACRO=TEMP_REACHED_STATE VARIABLE=bed_announced VALUE=0
        M118 Bed: target 0C
    {% endif %}

[gcode_macro M191]
gcode:
    {% if printer["heater_generic chamber"] is defined %}
        {% set s = params.S|float %}

        M141 {% for p in params %}{'%s%s' % (p, params[p])}{% endfor %}
        {% if s != 0 %}
            SET_GCODE_VARIABLE MACRO=TEMP_REACHED_STATE VARIABLE=chamber_announced VALUE=0
            UPDATE_DELAYED_GCODE ID=CHAMBER_REACHED_WATCH DURATION=0
            { action_respond_info("Chamber: waiting for " ~ s ~ "C") }
            TEMPERATURE_WAIT SENSOR="heater_generic chamber" MINIMUM={([s, 65]|min)-2}
            SET_GCODE_VARIABLE MACRO=TEMP_REACHED_STATE VARIABLE=chamber_announced VALUE=1
            { action_respond_info("Chamber: target " ~ ([s, 65]|min) ~ "C reached threshold, sensor " ~ (printer["heater_generic chamber"].temperature|round(1)) ~ "C") }
        {% endif %}
    {% endif %}

[gcode_macro M106]
gcode:
    {% set p = params.P|default(0)|int %}

    {% if p == 2 %}
    {% if params.S is defined %}
        SET_FAN_SPEED FAN=auxiliary_cooling_fan SPEED={(params.S|float / 255.0)}
    {% else %}
        SET_FAN_SPEED FAN=auxiliary_cooling_fan SPEED=1
    {% endif %}
    {% endif %} 

    {% if p == 0 %}
    {% if params.S is defined %}
        SET_FAN_SPEED FAN=cooling_fan SPEED={(params.S|float / 255.0)}

    {% else %}
        SET_FAN_SPEED FAN=cooling_fan SPEED=1
    {% endif %}
    {% endif %} 

    {% if p == 3 %}
    {% if params.S is defined %}
        SET_FAN_SPEED FAN=chamber_circulation_fan SPEED={(params.S|float / 255.0)}
    {% else %}
        SET_FAN_SPEED FAN=chamber_circulation_fan SPEED=1
    {% endif %}
    {% endif %} 

[gcode_macro M107]
gcode:  
    SET_FAN_SPEED FAN=cooling_fan SPEED=0

[gcode_macro M303]
gcode:
    {% if params.E is defined %}
     {% if params.S is defined %}
        {% if (params.E|int)==-1 %} 
         PID_CALIBRATE HEATER=heater_bed TARGET={params.S|int}
        {% endif %}
        {% if (params.E|int)==0 %}
         PID_CALIBRATE HEATER=extruder TARGET={params.S|int}
        {% endif %}
     {% endif %}
  {% endif %}

[gcode_macro M8029]
gcode:
     {% if params.D is defined %}
       {% if (params.D|int)==1 %} 
        ENABLE_FILAMENT_WIDTH_SENSOR
       {% endif %}
       {% if (params.D|int)==0 %} 
        DISABLE_FILAMENT_WIDTH_SENSOR
       {% endif %}
     {% endif %}

[gcode_macro M900]
gcode:
    {% if params.K is defined %} 
          SET_PRESSURE_ADVANCE ADVANCE={params.K}
    {% endif %}  
    {% if params.T is defined %}    
       SET_PRESSURE_ADVANCE SMOOTH_TIME={params.T}
    {% endif %} 

[gcode_macro M290]
gcode:
   SET_GCODE_OFFSET Z_ADJUST={params.Z}

[gcode_macro M901]
gcode:
    G28
    SHAPER_CALIBRATE
    M118 Input shaping complete
    SAVE_CONFIG

[gcode_macro M0]
gcode:
    PAUSE

[gcode_macro M25]
rename_existing: M9925
gcode:
    PAUSE

[gcode_macro RESPOND_INFO]
variable_S:0
gcode:
    {% if params.S is defined %}
        {% set s = params.S|int %}
        {% if s == 0 %}
            { action_respond_info("Nozzle cooled")  }
        {% endif %}
    {% endif %}

[gcode_macro M4027]
gcode:
    G1 X{150 - printer.probe["x_offset"]} Y{150 - printer.probe["y_offset"]} F9000
    probe
    SAVE_Z_OFFSET_TO_BED_MESH
    G1 z10 F600
    SET_GCODE_OFFSET Z=0 MOVE=1
    BED_MESH_CALIBRATE
    G0 Z50 F600
    G0 X0 Y0 F9000
    M400
    M118 Bed mesh calibrate complete
    SAVE_CONFIG

[gcode_macro M4028]
gcode:
    G28 
    get_zoffset
    M400
    M118 Position init complete

[gcode_macro M4029]
gcode:
    M104 S140
    SAVE_VARIABLE VARIABLE=z_offset VALUE=0
    G28 
    M400
    M118 Position init complete

    CLEAR_NOZZLE HOTEND=280
    G28
    get_zoffset

[gcode_macro M4030]
gcode:    
    BED_MESH_CLEAR      
    SET_GCODE_OFFSET Z=0 MOVE=0
    G28
    get_zoffset
    G1 X150 Y150 F9000
    G1 Z0 F600

[gcode_macro M4031]
gcode:
    SET_KINEMATIC_POSITION Z=20
    G1 Z30 F300
    SET_TMC_CURRENT STEPPER=stepper_z CURRENT={printer.configfile.settings['tmc2209 stepper_z'].run_current * 0.7 }
    SET_TMC_CURRENT STEPPER=stepper_z1 CURRENT={printer.configfile.settings['tmc2209 stepper_z1'].run_current * 0.7 }
    REVERSE_HOMING
    SET_TMC_CURRENT STEPPER=stepper_z CURRENT={printer.configfile.settings['tmc2209 stepper_z'].run_current}
    SET_TMC_CURRENT STEPPER=stepper_z1 CURRENT={printer.configfile.settings['tmc2209 stepper_z1'].run_current}
    G91
    G1 Z-30 F600
    G90

    SET_TMC_CURRENT STEPPER=stepper_z CURRENT={printer.configfile.settings['tmc2209 stepper_z'].run_current * 0.7 }
    SET_TMC_CURRENT STEPPER=stepper_z1 CURRENT={printer.configfile.settings['tmc2209 stepper_z1'].run_current * 0.7 }
    REVERSE_HOMING
    SET_TMC_CURRENT STEPPER=stepper_z CURRENT={printer.configfile.settings['tmc2209 stepper_z'].run_current}
    SET_TMC_CURRENT STEPPER=stepper_z1 CURRENT={printer.configfile.settings['tmc2209 stepper_z1'].run_current}
    G91
    G1 Z-30 F600
    G90

[gcode_macro M603]
description: Unload filament
gcode:
    {% set hotendtemp = params.S|default(250)|int %}
    {% set accel = printer.toolhead.max_accel|int %}
    DISABLE_ALL_SENSOR
    _CXY28
    M204 S8800
    G1 Y150 F9000
    G1 X305 F9000
    G1 Y20 F9000
    G1 Y5 F3000
    G4 P500
    G1 Y20 F9000
    G1 Y5 F3000
    G4 P500
    G1 Y20 F9000

    G1 X56 F12000
    G1 Y310 F12000
    G1 Y324 F600
    G1 X95 F600

    M106 S0
    M109 S{hotendtemp}
    M118 Heat up complete

    G92 E0
    G1 E5 F50
    G1 E50 F200
    G92 E0
    G1 E-0.8 F200
    G4 P300

    M106 S255
    M104 S{hotendtemp-100}
    G4 P5000

    G1 Y318 F9000
    G1 Y322 F600
    G1 Y318 F9000
    G1 Y322 F600
    G1 Y308 F30000
    G1 Y324 F600

    M106 S0
    M400
    M204 S{accel}
    M118 Unload finish

[gcode_macro M604]
description: Load filament
gcode:
    {% set hotendtemp = params.S|default(250)|int %}
    {% set current_state = params.F|default(1)|int %}
    {% set accel = printer.toolhead.max_accel|int %}
    DISABLE_ALL_SENSOR
    M204 S8800
    M104 S{hotendtemp}
    _CXY28
    {% if current_state == 1 %}
        {% if (printer.gcode_move.position.y) > 300 %}
            G91
            G1 Y-20 F9000
            G90
        {% endif %}
        G1 X95 F12000
        G1 Y312 F12000
        G1 Y316 F600
        G1 Y320 F9000
        G1 Y324 F600
    {% endif %}
    M109 S{hotendtemp}
    M118 Heat up complete

    G1 X95 F600
    G1 Y324 F600
    G92 E0
    G1 E5 F50
    G92 E0
    G1 E120 F300
    G92 E0
    G1 E-0.8 F200
    G4 P300

    M106 S255
    M104 S{hotendtemp-100}
    G4 P5000

    G1 Y318 F9000
    G1 Y322 F600
    G1 Y318 F9000
    G1 Y322 F600
    G1 Y308 F30000
    G1 Y324 F600

    M106 S0
    SET_FILAMENT_SENSOR SENSOR=fila ENABLE=1
    M400
    M204 S{accel}
    M118 Load finish

[output_pin sound]
pin:PA1
value:0

[gcode_macro beep_on]
gcode:
    SET_PIN PIN=sound VALUE=1

[gcode_macro beep_off]
gcode:
    SET_PIN PIN=sound VALUE=0

[gcode_arcs]
resolution: 1.0

[gcode_macro M109]
rename_existing: M99109
gcode:
    {% set s = params.S|float %}

    M104 {% for p in params %}{'%s%s' % (p, params[p])}{% endfor %}
    {% if s != 0 %}
        TEMPERATURE_WAIT SENSOR=extruder MINIMUM={s} MAXIMUM={s+1}
    {% endif %}

[exclude_object]

[gcode_macro G31]
gcode:
    SET_GCODE_VARIABLE MACRO=G29 VARIABLE=k VALUE=1

[gcode_macro G32]
gcode:
    SET_GCODE_VARIABLE MACRO=G29 VARIABLE=k VALUE=0

[gcode_macro G29]
variable_k: 1
gcode:
    {% set chamber_target = 0 %}
    {% if printer["heater_generic chamber"] is defined %}
        {% set chamber_target = printer["heater_generic chamber"].target|int %}
    {% endif %}

    {% if chamber_target > 0 %}
        M141 S0
        G4 P15000
        { action_respond_info("Chamber heater temporarily disabled for probing") }
    {% endif %}

    BED_MESH_CLEAR
    {% if k|int == 1 %}
        G28
        get_zoffset
        G1 X{150 - printer.probe["x_offset"]} Y{150 - printer.probe["y_offset"]} F9000
        G1 Z10 F600
        probe
        SAVE_Z_OFFSET_TO_BED_MESH
        G1 Z10 F600
        BED_MESH_CALIBRATE PROFILE=default
        SAVE_VARIABLE VARIABLE=profile_name VALUE='"default"'
        G4 P5000

        {% if chamber_target > 0 %}
            M141 S{chamber_target}
            { action_respond_info("Chamber heater restored to " ~ chamber_target ~ "C") }
        {% endif %}

        SAVE_CONFIG_QD
    {% else %}
        G28
        get_zoffset
        {% if printer["bed_mesh"].profiles.default %}
            BED_MESH_PROFILE LOAD=default
            SAVE_VARIABLE VARIABLE=profile_name VALUE='"default"'

            {% if chamber_target > 0 %}
                M141 S{chamber_target}
                { action_respond_info("Chamber heater restored to " ~ chamber_target ~ "C") }
            {% endif %}
        {% else %}
            G1 X{150 - printer.probe["x_offset"]} Y{150 - printer.probe["y_offset"]} F9000
            G1 Z10 F600
            probe
            SAVE_Z_OFFSET_TO_BED_MESH
            G1 Z10 F600
            _BED_MESH_CALIBRATE PROFILE=default
            G4 P5000

            {% if chamber_target > 0 %}
                M141 S{chamber_target}
                { action_respond_info("Chamber heater restored to " ~ chamber_target ~ "C") }
            {% endif %}

            SAVE_CONFIG_QD
        {% endif %}
    {% endif %}

[gcode_macro M204]
rename_existing: M99204
gcode:
    {% if params.S is defined %}
        {% set s = params.S|float %}
    {% endif %}
    {% if params.P is defined %}
    {% if params.T is defined %}
        {% set s = [params.P|float ,params.T|float] | min %}
    {% endif %}
    {% endif %}

    SET_VELOCITY_LIMIT ACCEL={s}
    SET_VELOCITY_LIMIT ACCEL_TO_DECEL={s/2}

[gcode_macro Z_VIBRATE]
gcode:
    m204 S400
    G90
    G0 Z4
    G91
   #G4 P3000
     SET_PIN PIN=ctlyd VALUE=1 
    {% for z in range(1,50) %}
        G1 Z1 F1200
#        G4 P50
        G1 Z-1 F1200
#       G4 P50
    {% endfor %}
    M204 S100
    SET_PIN PIN=ctlyd VALUE=0
    G4 P1000
    G1 Z4
    G90

[gcode_macro TEST_POSTPRINT_EXHAUST]
description: Test PRINT_END exhaust flag behavior without running full PRINT_END
gcode:
    {% set enabled = params.ENABLED|default(1)|int %}
    {% set duration = params.DURATION|default(30)|int %}

    SET_GCODE_VARIABLE MACRO=PRINT_END VARIABLE=postprint_chamber_exhaust VALUE={enabled}
    { action_respond_info("TEST: wrote PRINT_END.postprint_chamber_exhaust=" ~ enabled) }

    {% if enabled == 1 %}
        { action_respond_info("TEST: starting postprint chamber exhaust for " ~ duration ~ "s") }
        START_POSTPRINT_CHAMBER_EXHAUST DURATION={duration}
    {% else %}
        { action_respond_info("TEST: stopping postprint chamber exhaust") }
        STOP_POSTPRINT_CHAMBER_EXHAUST
    {% endif %}

    SET_GCODE_VARIABLE MACRO=PRINT_END VARIABLE=postprint_chamber_exhaust VALUE=0
    { action_respond_info("TEST: reset PRINT_END.postprint_chamber_exhaust=0") }

[gcode_macro QIDI_BED_LEVEL_60]
description: Heat bed to 60C for PLA, PLA+, and most TPU, then run optimized 9x9 QIDI-style bed level
gcode:
    { action_respond_info("Heating bed to 60C for QIDI bed level: PLA / PLA+ / most TPU") }

    # Reduce extra sensor/heater/fan activity during bed probing.
    DISABLE_ALL_SENSOR
    M141 S0
    DISABLE_BOX_HEATER
    M106 S0
    M106 P2 S0

    # Heat bed and wait with TEMPERATURE_WAIT.
    M140 S60
    TEMPERATURE_WAIT SENSOR=heater_bed MINIMUM=59.8

    # QIDI prep: home, clear nozzle, home again, then get_zoffset.
    M4029

    # Clear old mesh before writing the new default mesh.
    BED_MESH_CLEAR

    # Save current QIDI z-offset into the mesh baseline.
    G1 X{150 - printer.probe["x_offset"]} Y{150 - printer.probe["y_offset"]} F9000
    G1 Z10 F600
    probe
    SAVE_Z_OFFSET_TO_BED_MESH
    G1 Z10 F600

    # Keep the stock 9x9 mesh density, but avoid the duplicated G31/G29 chain.
    _BED_MESH_CALIBRATE PROFILE=default PROBE_COUNT=9,9

    SAVE_VARIABLE VARIABLE=profile_name VALUE='"default"'
    G4 P5000
    SAVE_CONFIG_QD


[gcode_macro QIDI_BED_LEVEL_80]
description: Heat bed to 80C for PETG and some flexible materials, then run optimized 9x9 QIDI-style bed level
gcode:
    { action_respond_info("Heating bed to 80C for QIDI bed level: PETG / some flexibles") }

    # Reduce extra sensor/heater/fan activity during bed probing.
    DISABLE_ALL_SENSOR
    M141 S0
    DISABLE_BOX_HEATER
    M106 S0
    M106 P2 S0

    # Heat bed and wait with TEMPERATURE_WAIT.
    M140 S80
    TEMPERATURE_WAIT SENSOR=heater_bed MINIMUM=79.8

    # QIDI prep: home, clear nozzle, home again, then get_zoffset.
    M4029

    # Clear old mesh before writing the new default mesh.
    BED_MESH_CLEAR

    # Save current QIDI z-offset into the mesh baseline.
    G1 X{150 - printer.probe["x_offset"]} Y{150 - printer.probe["y_offset"]} F9000
    G1 Z10 F600
    probe
    SAVE_Z_OFFSET_TO_BED_MESH
    G1 Z10 F600

    # Keep the stock 9x9 mesh density, but avoid the duplicated G31/G29 chain.
    _BED_MESH_CALIBRATE PROFILE=default PROBE_COUNT=9,9

    SAVE_VARIABLE VARIABLE=profile_name VALUE='"default"'
    G4 P5000
    SAVE_CONFIG_QD


[gcode_macro QIDI_BED_LEVEL_100]
description: Heat bed to 100C for ASA and ABS, then run optimized 9x9 QIDI-style bed level
gcode:
    { action_respond_info("Heating bed to 100C for QIDI bed level: ASA / ABS") }

    # Reduce extra sensor/heater/fan activity during bed probing.
    DISABLE_ALL_SENSOR
    M141 S0
    DISABLE_BOX_HEATER
    M106 S0
    M106 P2 S0

    # Heat bed and wait with TEMPERATURE_WAIT.
    M140 S100
    TEMPERATURE_WAIT SENSOR=heater_bed MINIMUM=99.8

    # QIDI prep: home, clear nozzle, home again, then get_zoffset.
    M4029

    # Clear old mesh before writing the new default mesh.
    BED_MESH_CLEAR

    # Save current QIDI z-offset into the mesh baseline.
    G1 X{150 - printer.probe["x_offset"]} Y{150 - printer.probe["y_offset"]} F9000
    G1 Z10 F600
    probe
    SAVE_Z_OFFSET_TO_BED_MESH
    G1 Z10 F600

    # Keep the stock 9x9 mesh density, but avoid the duplicated G31/G29 chain.
    _BED_MESH_CALIBRATE PROFILE=default PROBE_COUNT=9,9

    SAVE_VARIABLE VARIABLE=profile_name VALUE='"default"'
    G4 P5000
    SAVE_CONFIG_QD


[gcode_macro QIDI_BED_LEVEL_110]
description: Heat bed to 110C for PC and other high-temp engineering filaments, then run optimized 9x9 QIDI-style bed level
gcode:
    { action_respond_info("Heating bed to 110C for QIDI bed level: PC / high-temp engineering filaments") }

    # Reduce extra sensor/heater/fan activity during bed probing.
    DISABLE_ALL_SENSOR
    M141 S0
    DISABLE_BOX_HEATER
    M106 S0
    M106 P2 S0

    # Heat bed and wait with TEMPERATURE_WAIT.
    M140 S110
    TEMPERATURE_WAIT SENSOR=heater_bed MINIMUM=109.8

    # QIDI prep: home, clear nozzle, home again, then get_zoffset.
    M4029

    # Clear old mesh before writing the new default mesh.
    BED_MESH_CLEAR

    # Save current QIDI z-offset into the mesh baseline.
    G1 X{150 - printer.probe["x_offset"]} Y{150 - printer.probe["y_offset"]} F9000
    G1 Z10 F600
    probe
    SAVE_Z_OFFSET_TO_BED_MESH
    G1 Z10 F600

    # Keep the stock 9x9 mesh density, but avoid the duplicated G31/G29 chain.
    _BED_MESH_CALIBRATE PROFILE=default PROBE_COUNT=9,9

    SAVE_VARIABLE VARIABLE=profile_name VALUE='"default"'
    G4 P5000
    SAVE_CONFIG_QD

[gcode_macro _QIDI_FAIL_CLOSED]
description: Fail closed after virtual_sdcard/probe/startup error. No motion.
gcode:
    M118 FAIL-CLOSED: print error detected; disabling heat/fans/sensors without motion

    TURN_OFF_HEATERS
    DISABLE_BOX_HEATER

    M106 S0
    M106 P0 S0
    M106 P2 S0

    UPDATE_DELAYED_GCODE ID=postprint_chamber_alert_15 DURATION=0
    UPDATE_DELAYED_GCODE ID=postprint_chamber_alert_30 DURATION=0
    UPDATE_DELAYED_GCODE ID=POSTPRINT_CHAMBER_FAN_OFF DURATION=0

    SET_GCODE_VARIABLE MACRO=PRINT_END VARIABLE=postprint_alerts_enabled VALUE=0
    SET_GCODE_VARIABLE MACRO=_HOMING_GUARD VARIABLE=active VALUE=0
    SET_GCODE_VARIABLE MACRO=_STARTUP_CANCEL_GUARD VARIABLE=active VALUE=0
    SET_GCODE_VARIABLE MACRO=_STARTUP_TOOL_GUARD VARIABLE=active VALUE=0
    SET_GCODE_VARIABLE MACRO=_STARTUP_TOOL_GUARD VARIABLE=tool VALUE=-1

    DISABLE_ALL_SENSOR
    BED_MESH_CLEAR

    SET_STEPPER_ENABLE STEPPER=stepper_x ENABLE=0
    SET_STEPPER_ENABLE STEPPER=stepper_y ENABLE=0
    SET_STEPPER_ENABLE STEPPER=stepper_z ENABLE=1
    SET_STEPPER_ENABLE STEPPER=stepper_z1 ENABLE=1
    SET_STEPPER_ENABLE STEPPER=extruder ENABLE=0
